by-cx/raspik/photos/01.jpg

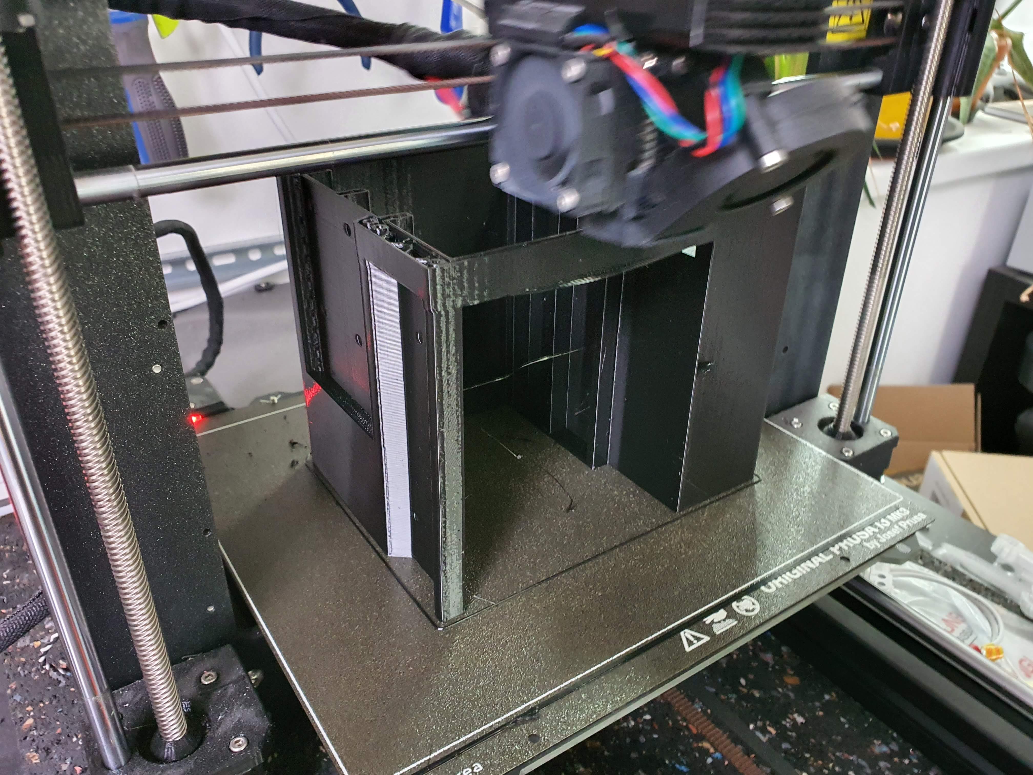
photos/01.jpg
