by-cx/raspik/photos/02.jpg

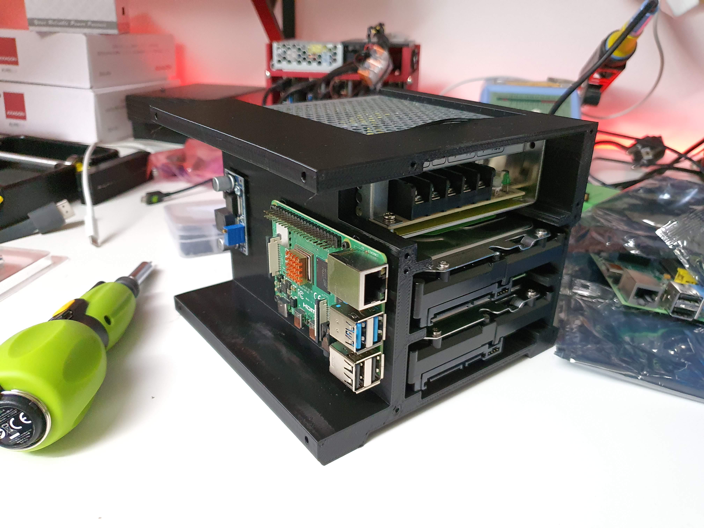
photos/02.jpg
