by-cx/raspik/photos/03.jpg

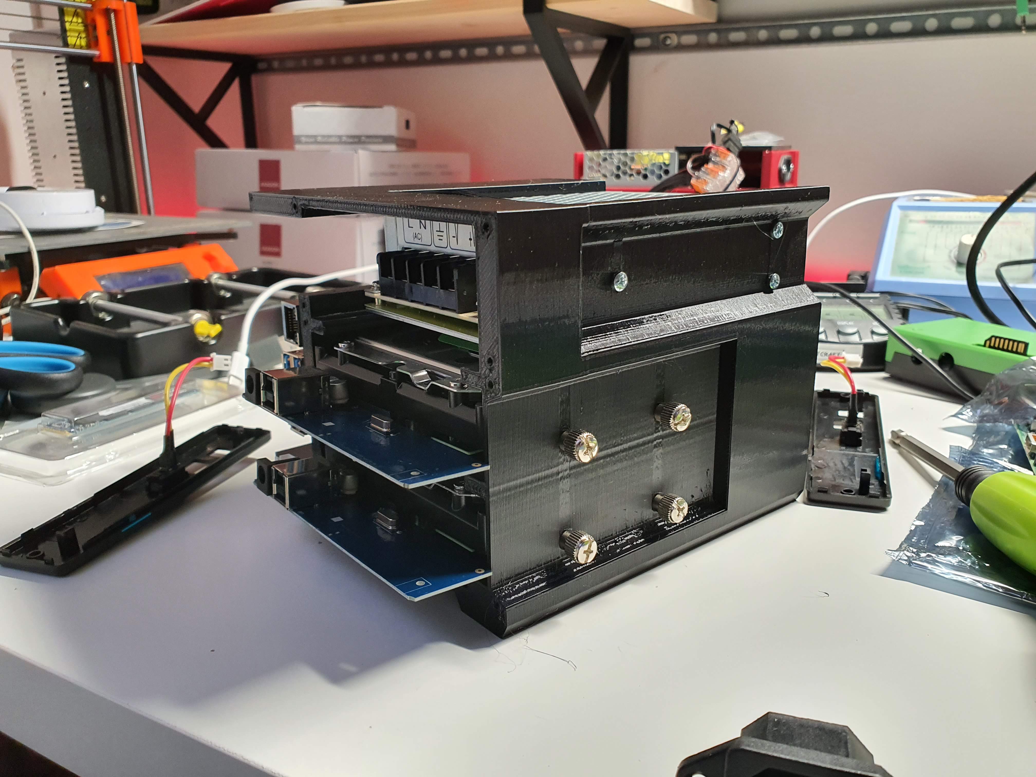
photos/03.jpg
