by-cx/raspik/photos/04.jpg

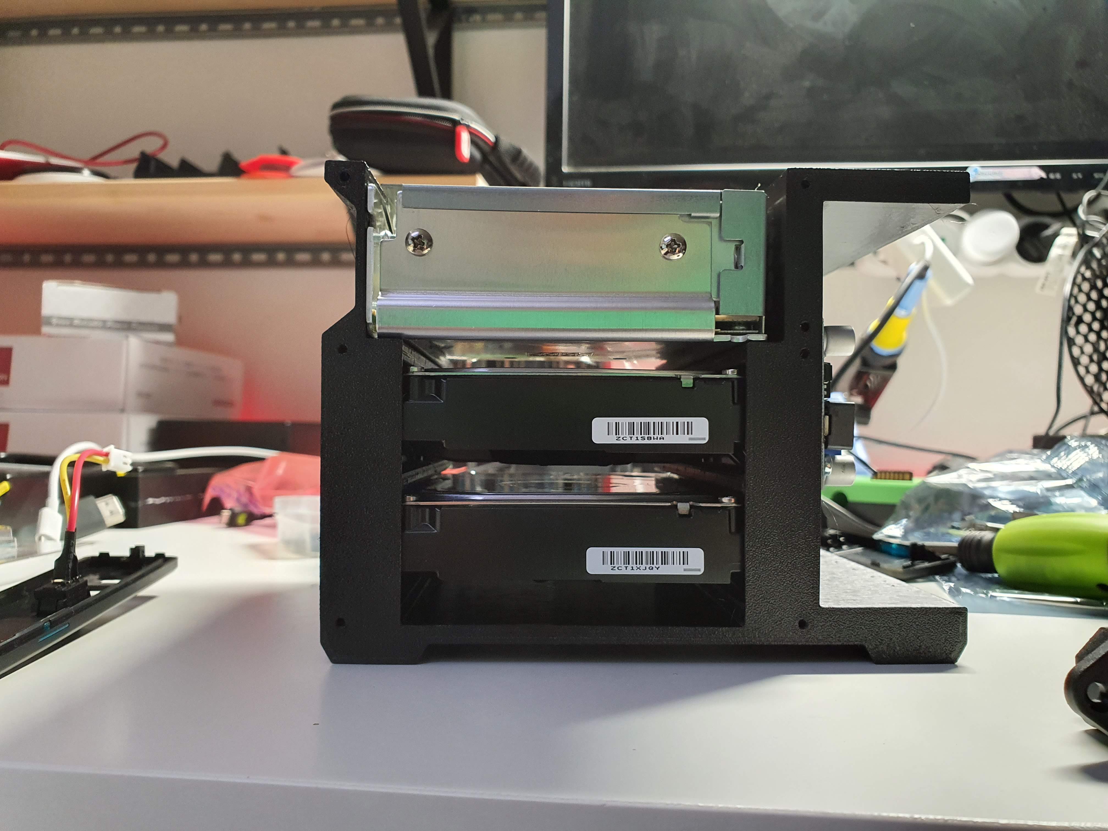
photos/04.jpg
