by-cx/raspik/photos/05.jpg

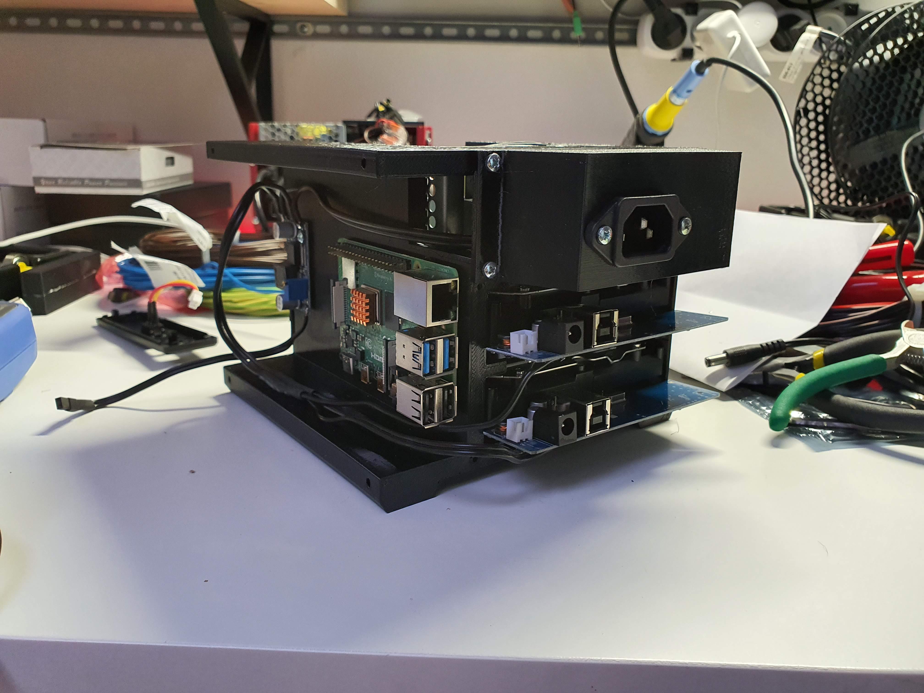
photos/05.jpg
