by-cx/raspik/photos/06.jpg

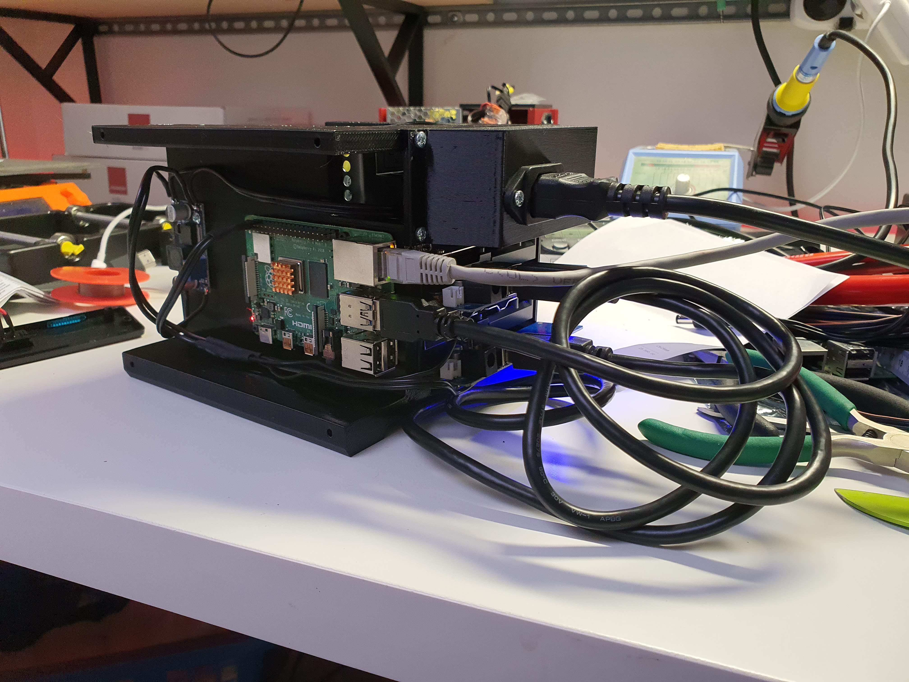
photos/06.jpg
