by-cx/raspik/photos/07.jpg

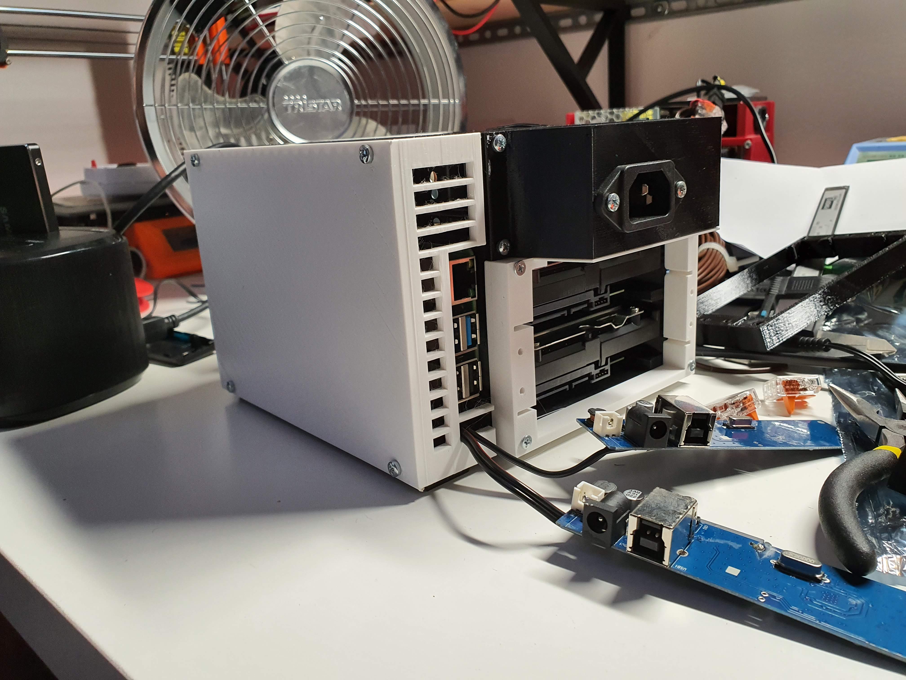
photos/07.jpg
