by-cx/raspik/photos/08.jpg

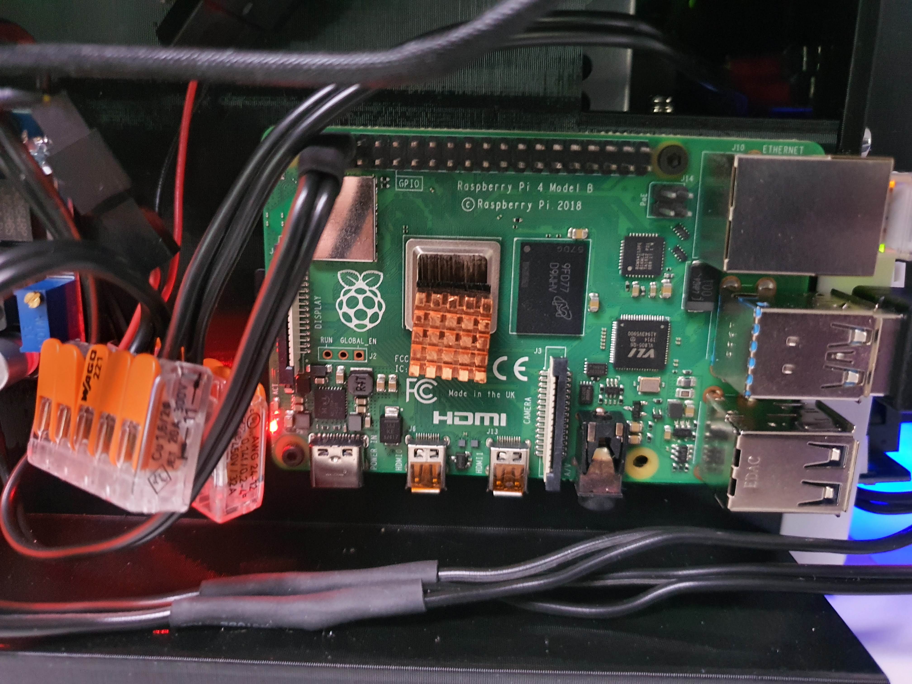
photos/08.jpg
