by-cx/raspik/photos/09.jpg

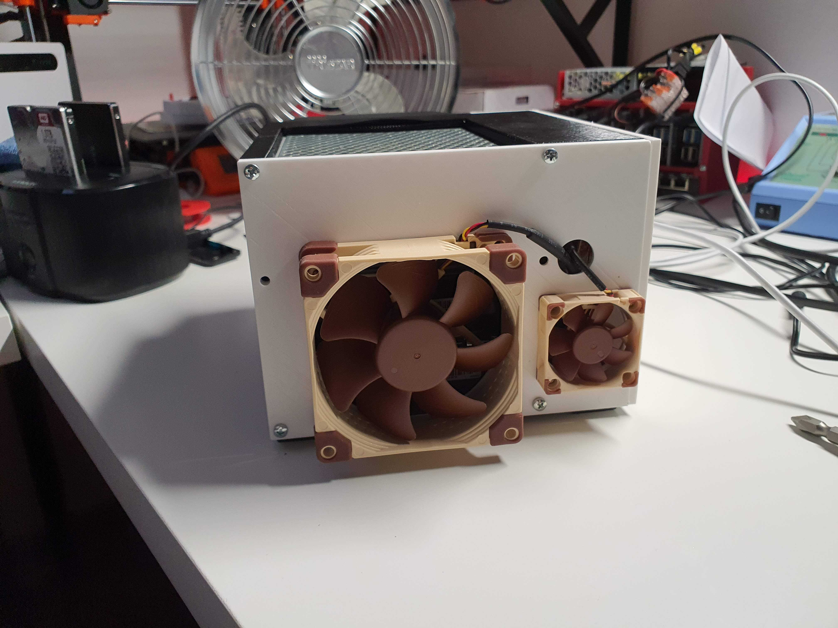
photos/09.jpg
