by-cx/raspik/photos/10.jpg

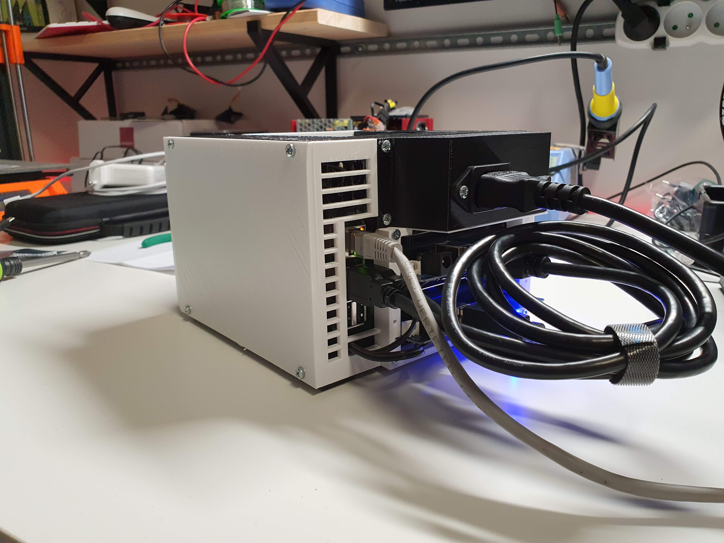
photos/10.jpg
