by-cx/raspik/photos/11.jpg

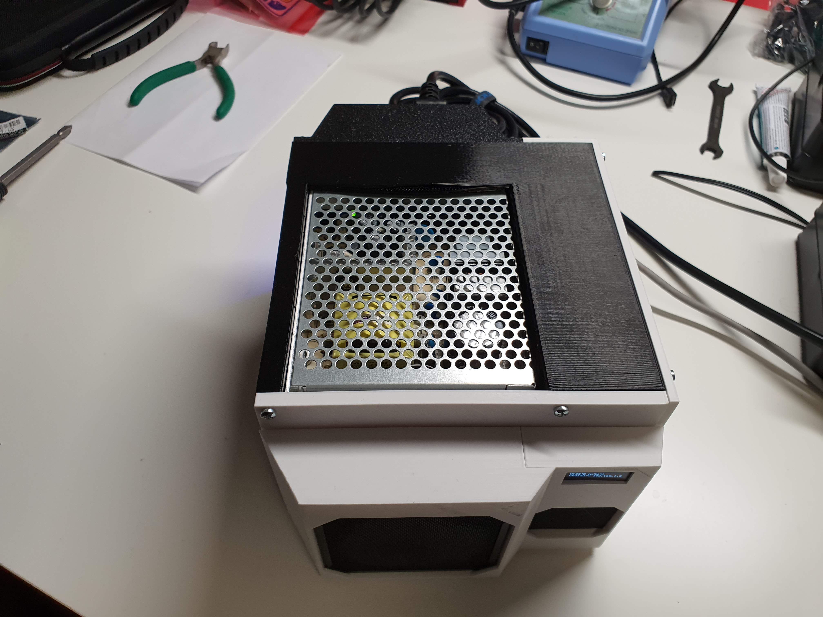
photos/11.jpg
