by-cx/raspik/photos/12.jpg

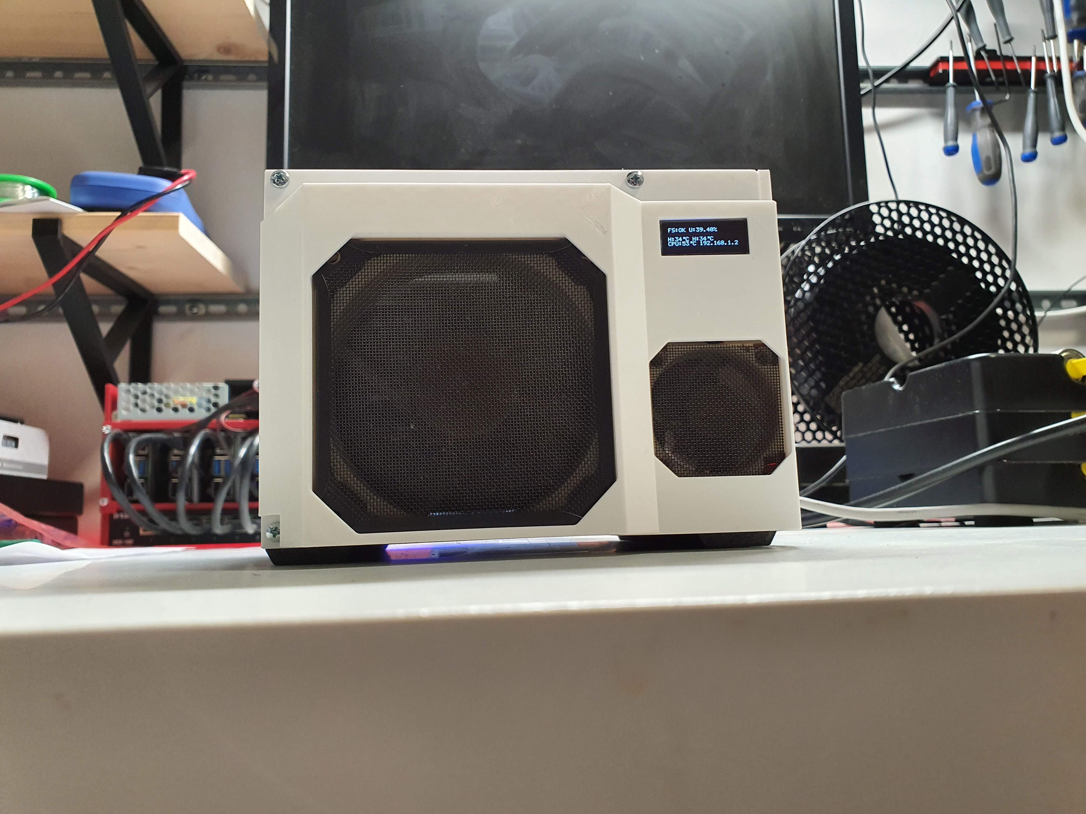
photos/12.jpg
