by-cx/raspik/photos/13.jpg

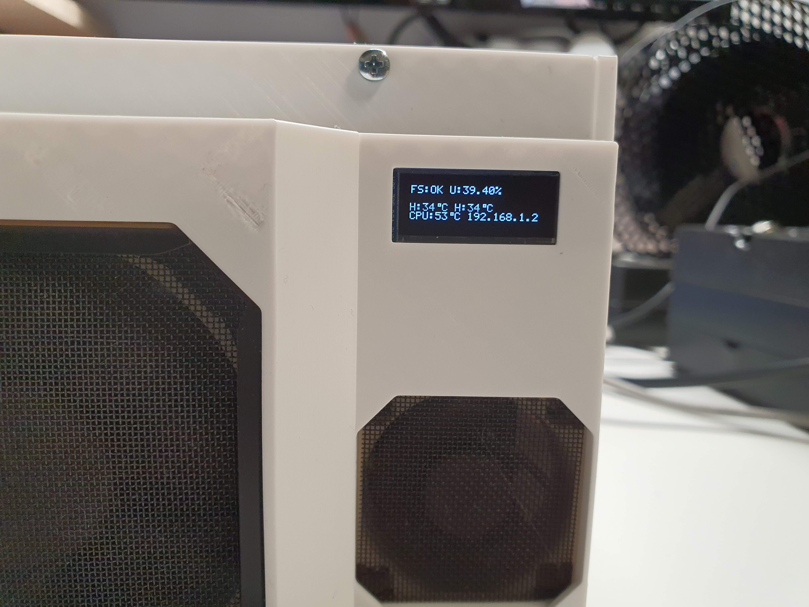
photos/13.jpg
