by-cx/raspik/photos/14.jpg

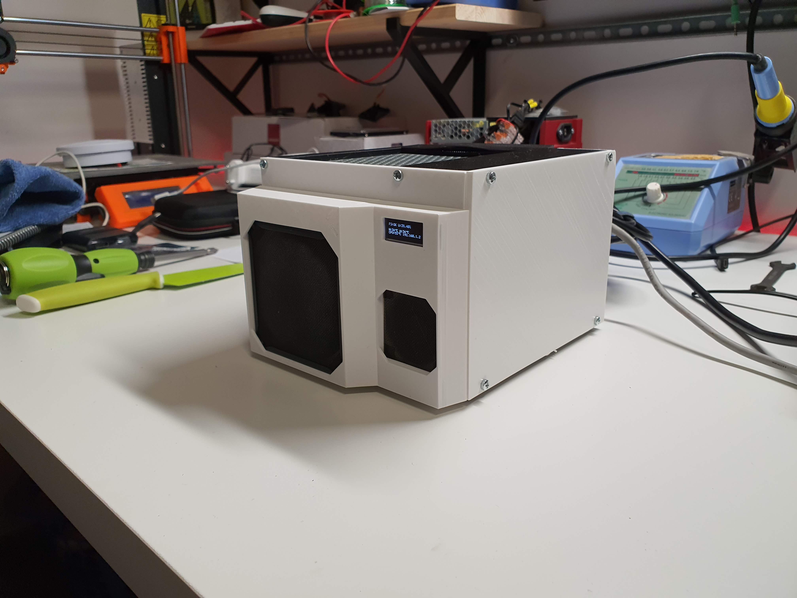
photos/14.jpg
