by-cx/raspik/photos/15.jpg

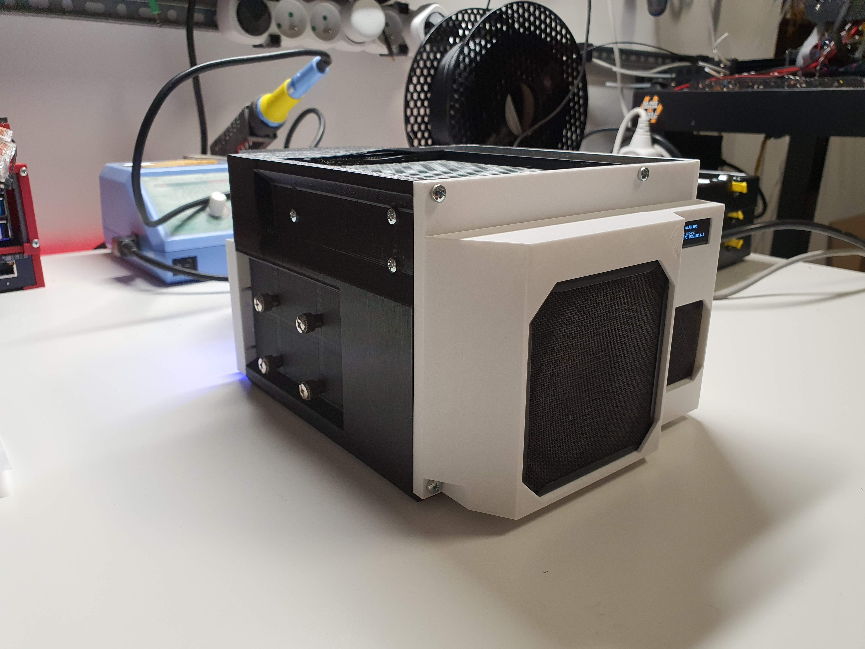
photos/15.jpg
